VogtD01/ClimbSafe/Präsentation_Diagramme/Bilder/IMG-20250129-WA0008.jpg

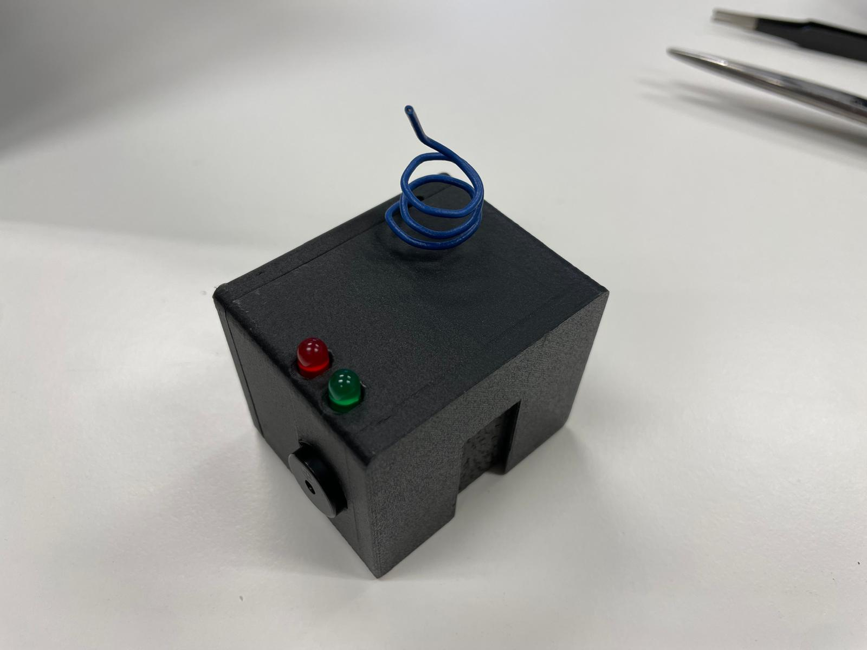
Präsentation_Diagramme/Bilder/IMG-20250129-WA0008.jpg
